serhaturtis/AC-Pitch-Black-Forest/outputs/images/back.png

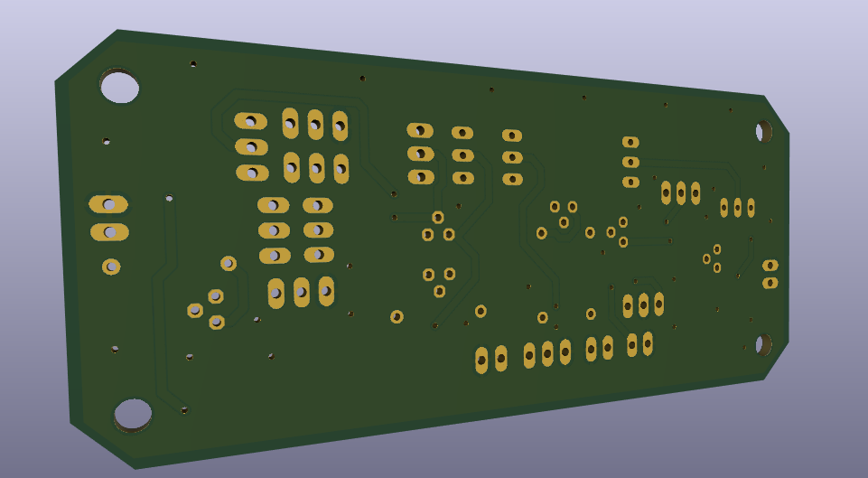
outputs/images/back.png
